solarmon/Greaseweazle/Greaseweazle F1 Plus Gotek Rev 1.1/Greaseweazle F1 Plus Gotek - PCB Bottom.png

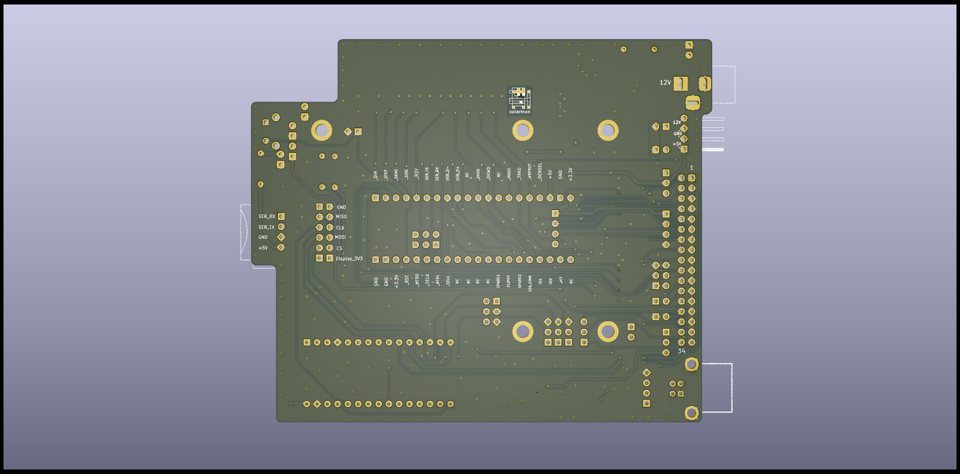
Greaseweazle F1 Plus Gotek Rev 1.1/Greaseweazle F1 Plus Gotek - PCB Bottom.png
