solarmon/Greaseweazle/Greaseweazle F1 Plus Rev 1.1/Greaseweazle F1 Plus - PCB SMT Bottom.png

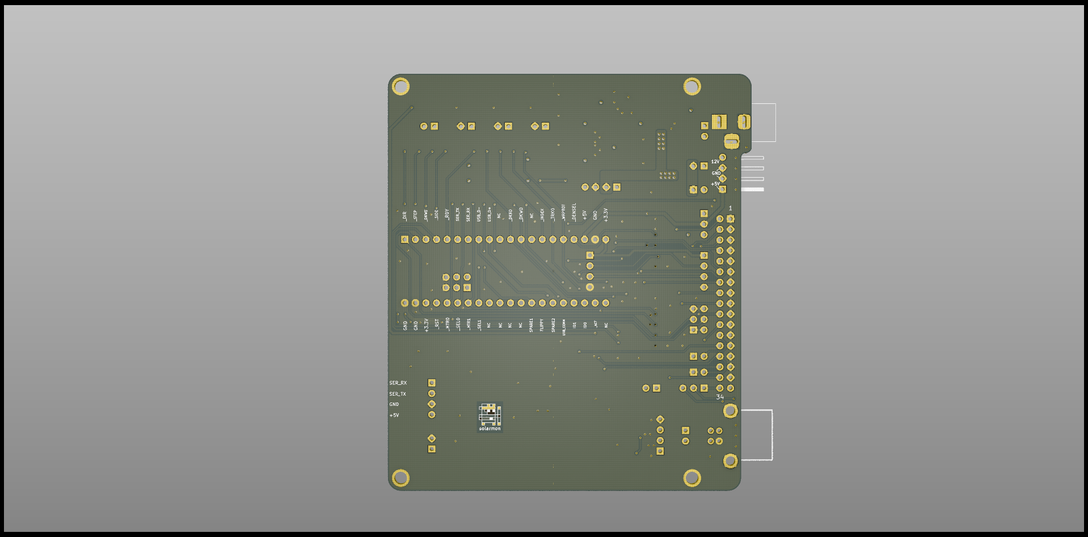
Greaseweazle F1 Plus Rev 1.1/Greaseweazle F1 Plus - PCB SMT Bottom.png
