solarmon/Greaseweazle/LEDC68 and 0.9 Inch OLED Adapter/LEDC68 and 0.9 Inch OLED Adapter.kicad_pcb

## KiCad design LEDC68 and 0.9 Inch OLED Adapter/LEDC68 and 0.9 Inch OLED Adapter.kicad_pcb (2021-04-10)

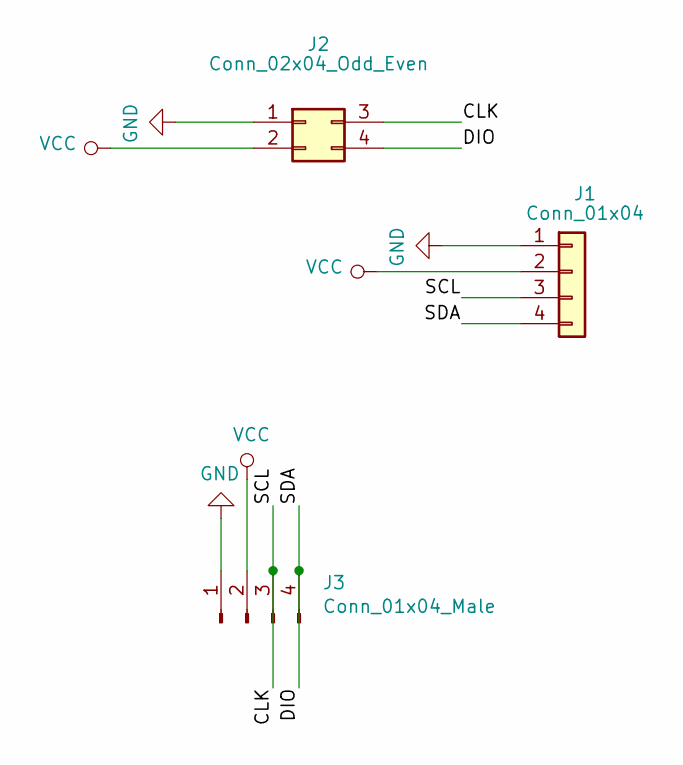
[picture p30: schematic LEDC68 and 0.9 Inch OLED Adapter.sch]

Parts:
J1: Conn_01x04; PinSocket_1x04_P2.54mm_Vertical
J2: Conn_02x04_Odd_Even; PinSocket_2x02_P2.54mm_Vertical
J3: Conn_01x04_Male; PinHeader_1x04_P2.54mm_Vertical

Connections:
/CLK: J1.3, J2.3, J3.3
/DIO: J1.4, J2.4, J3.4
GND: J1.1, J2.1, J3.1
VCC: J1.2, J2.2, J3.2

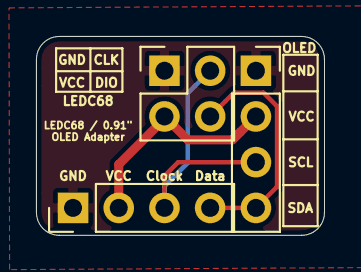
[picture p31: board LEDC68 and 0.9 Inch OLED Adapter.kicad_pcb from above]

Board: 2 copper layers, 16.0 x 11.0 mm, 3 parts (0 on the bottom side), 4 nets.
